ktarrant/environment-sensor/images/ESP32_profile.jpg

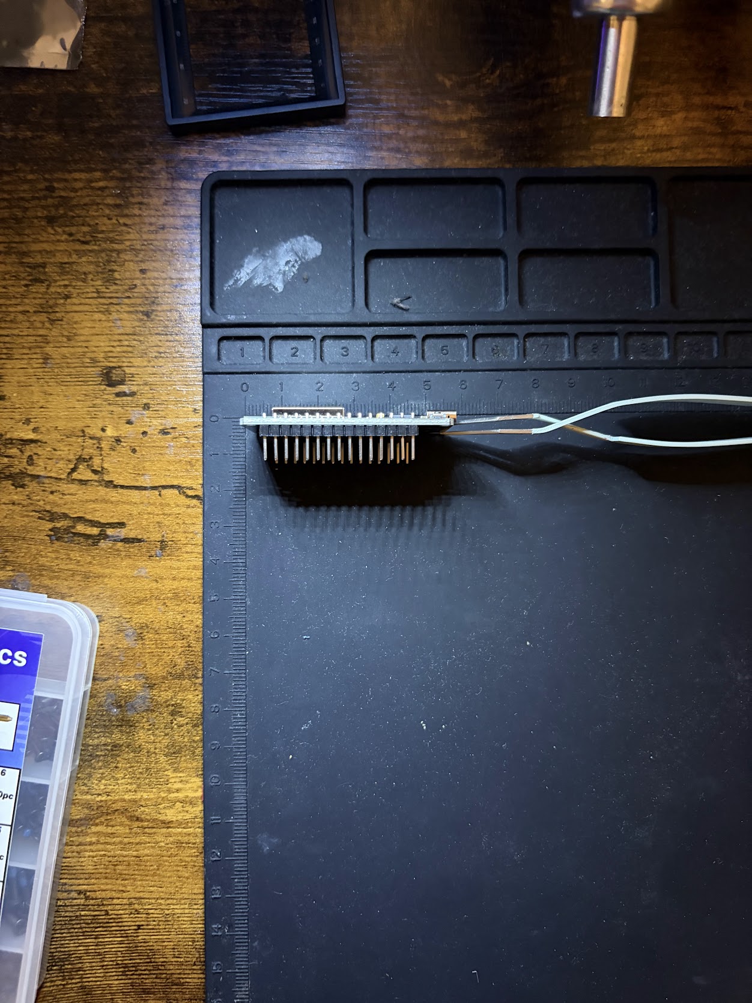
images/ESP32_profile.jpg
