ktarrant/environment-sensor/images/perfboard_4x6.png

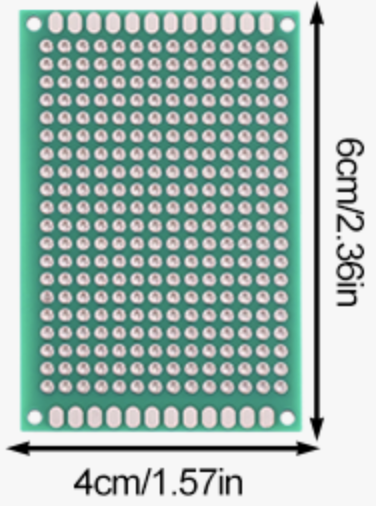
images/perfboard_4x6.png
