ktarrant/environment-sensor/images/perfboard_4x6_photo.jpg

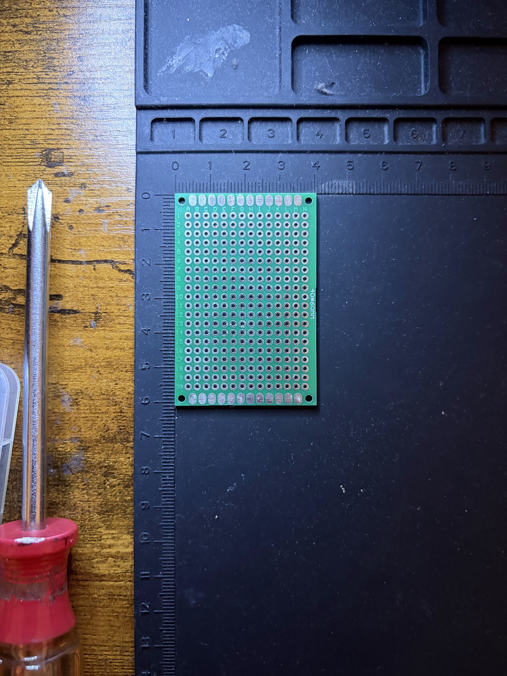
images/perfboard_4x6_photo.jpg
