ktarrant/environment-sensor/images/renders/enclosure_pod_iso.png

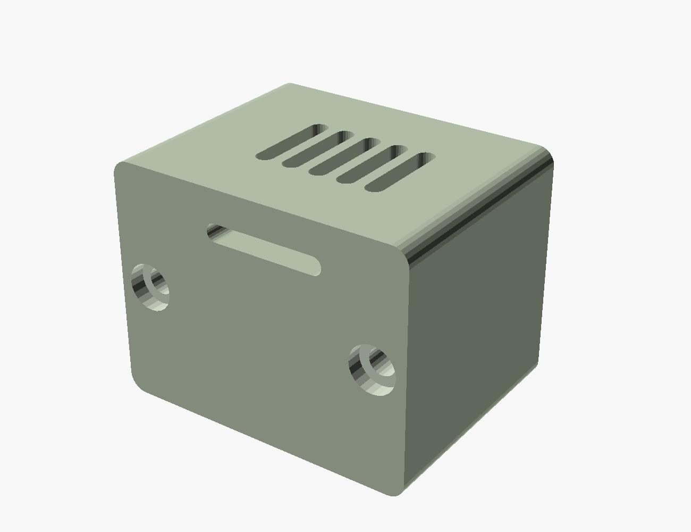
images/renders/enclosure_pod_iso.png
