ktarrant/environment-sensor/images/renders/esp32_iso.png

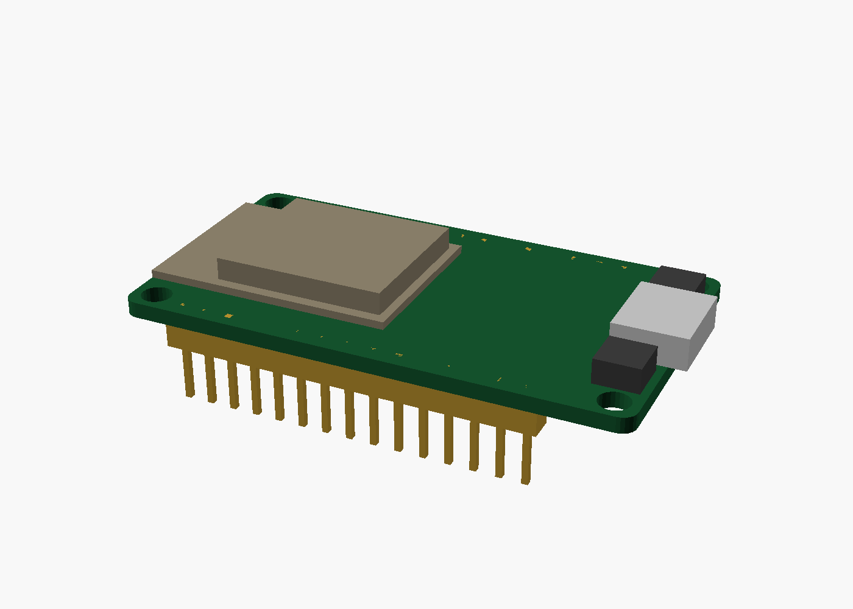
images/renders/esp32_iso.png
