ktarrant/environment-sensor/images/sensor_profile.jpg

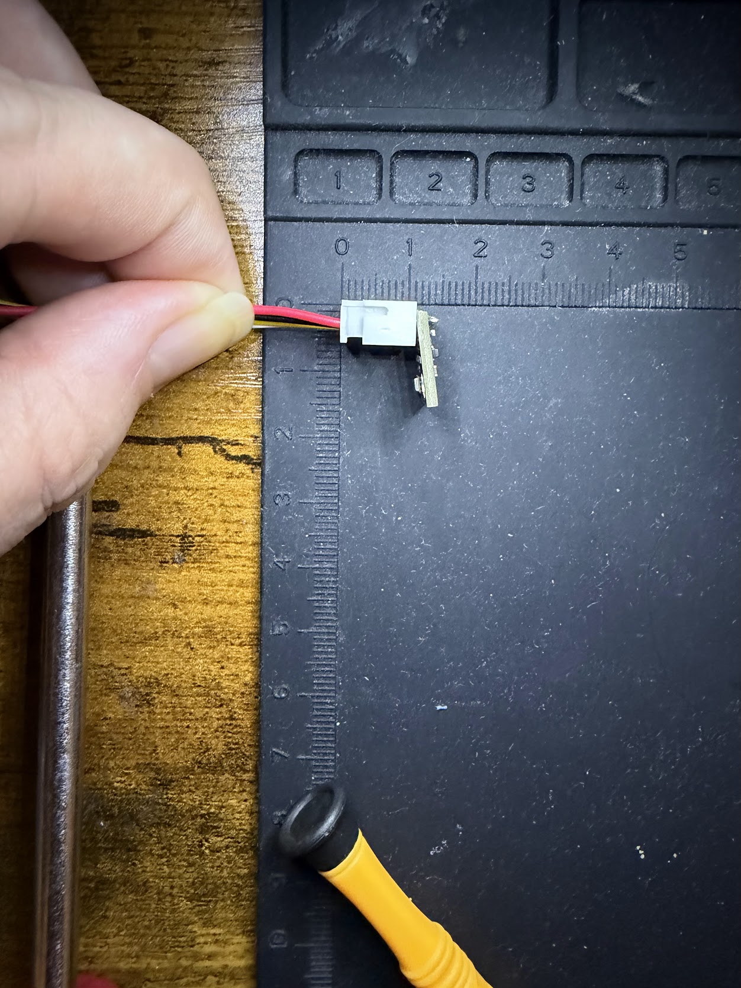
images/sensor_profile.jpg
