ktarrant/environment-sensor/images/esp32_assembled_profile.jpg

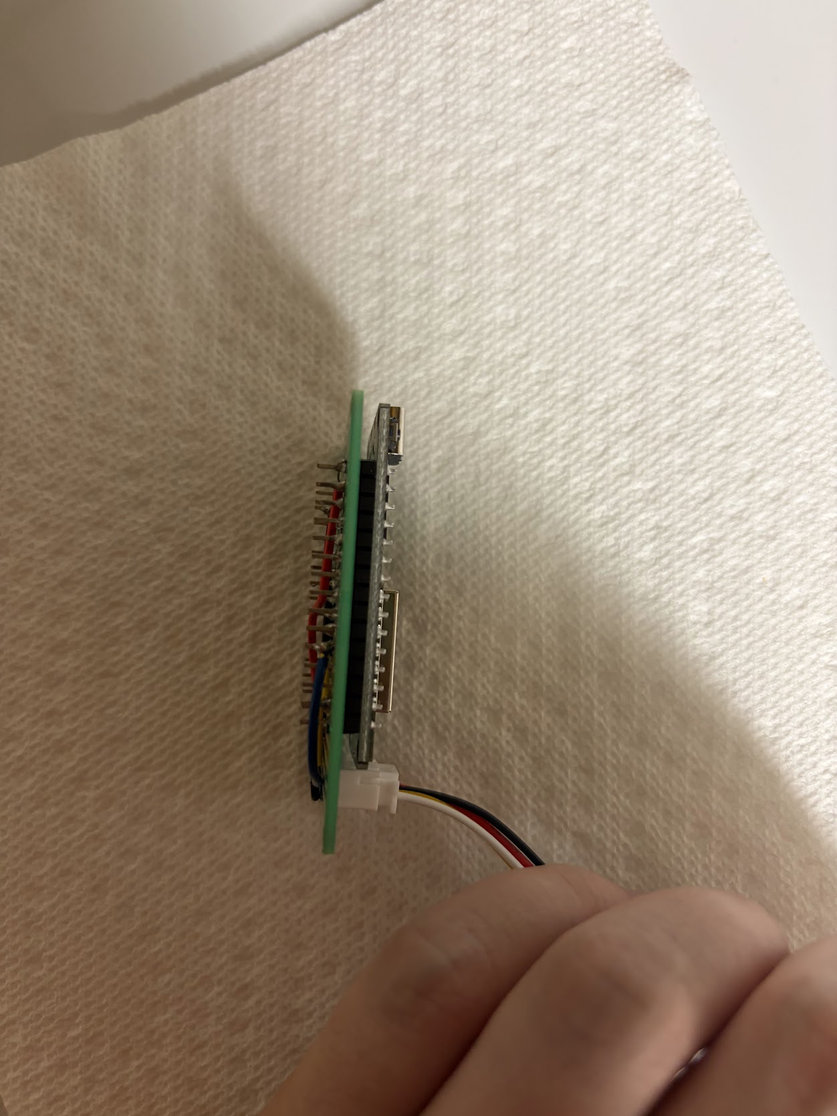
images/esp32_assembled_profile.jpg
