ktarrant/environment-sensor/images/esp32_assembled_top.jpg

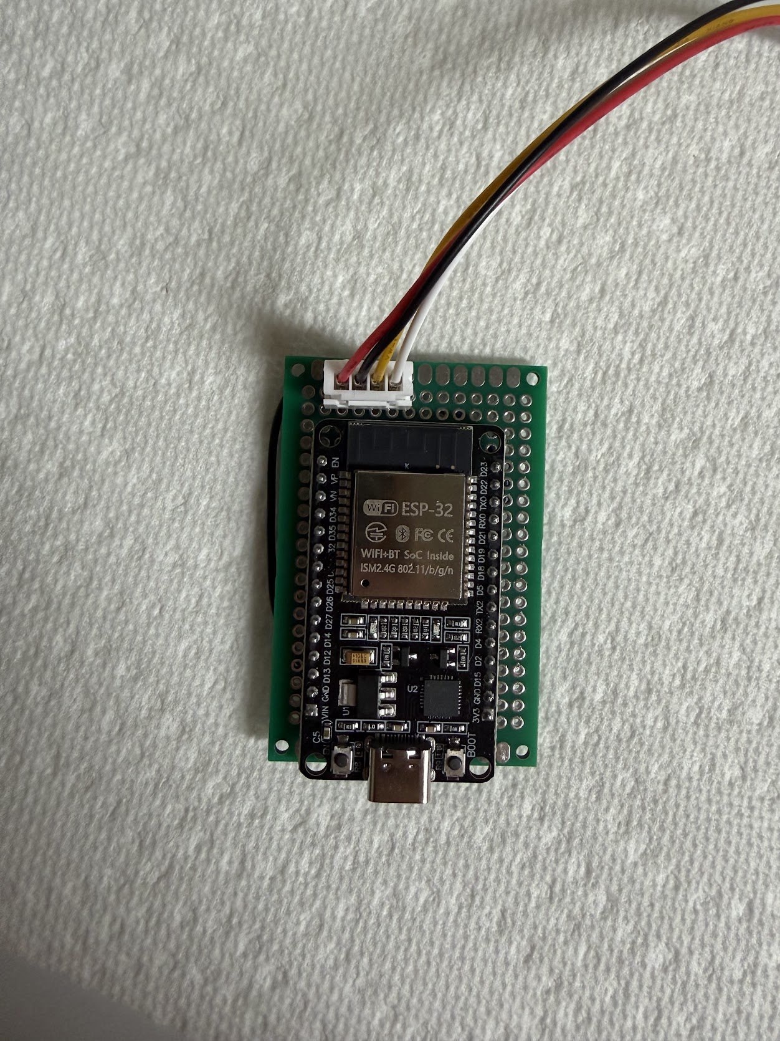
images/esp32_assembled_top.jpg
