ktarrant/environment-sensor/images/renders/assembly_iso.png

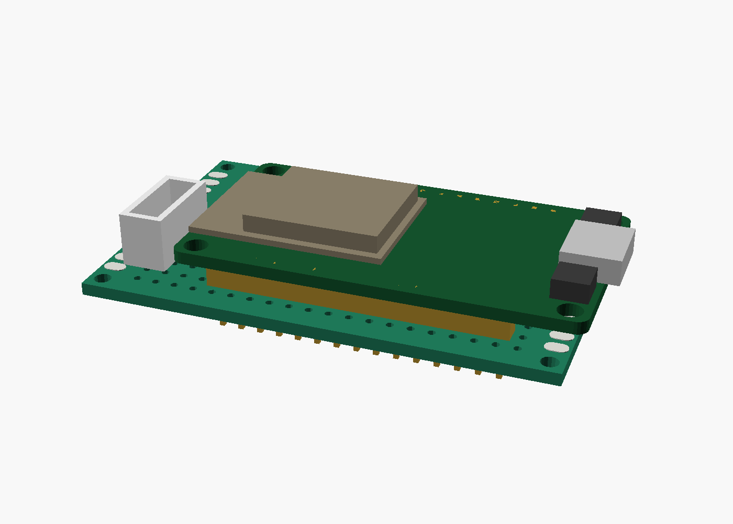
images/renders/assembly_iso.png
