ktarrant/environment-sensor/images/renders/assembly_top.png

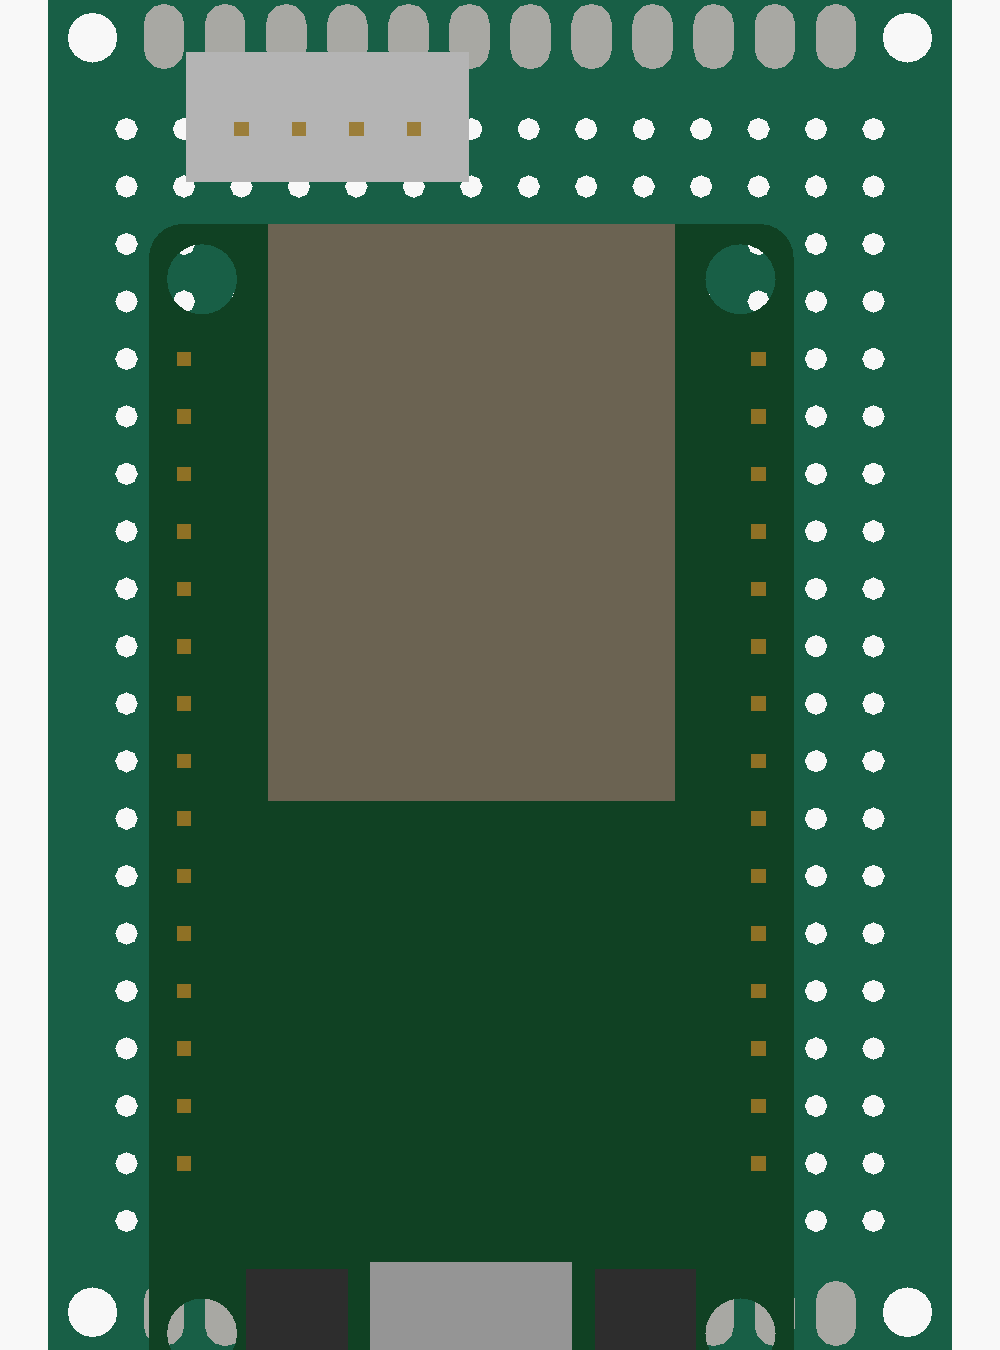
images/renders/assembly_top.png
