ktarrant/environment-sensor/images/renders/sensor_assembly_iso.png

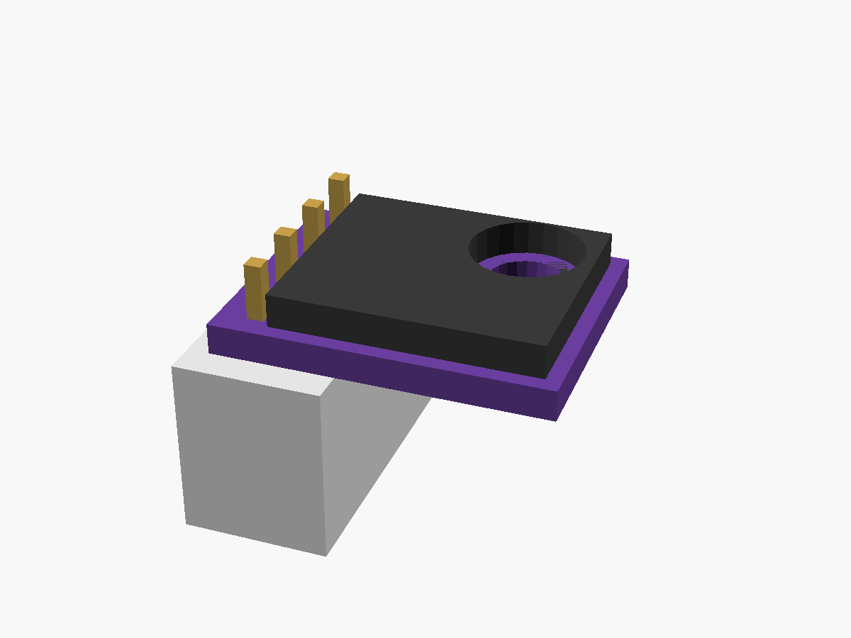
images/renders/sensor_assembly_iso.png
