ktarrant/environment-sensor/images/renders/sensor_assembly_top.png

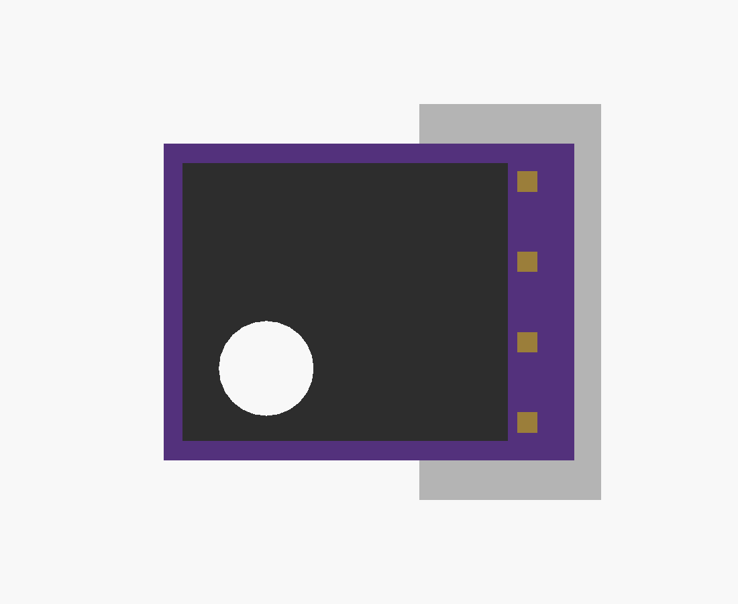
images/renders/sensor_assembly_top.png
